Jshulgach/Desktop-Arm/CAD Models/16-x-2-lcd-display-module/Lcd6.jpg

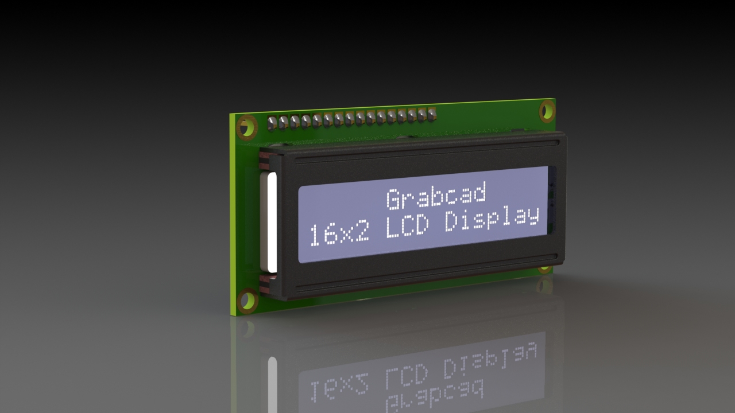
CAD Models/16-x-2-lcd-display-module/Lcd6.jpg
