Jshulgach/Desktop-Arm/CAD Models/ac-power-outlet-socket/AC Power Outlet Socket.PNG

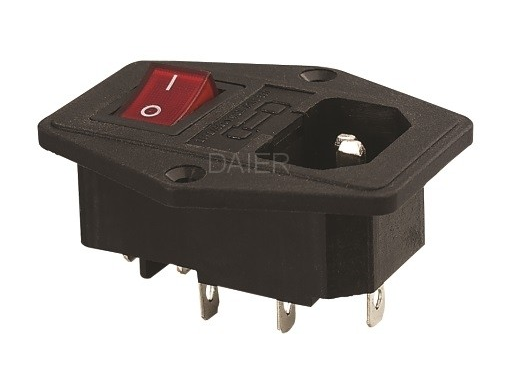
CAD Models/ac-power-outlet-socket/AC Power Outlet Socket.PNG
