Jshulgach/Desktop-Arm/CAD Models/arduino-mega-ramps-1-4/ARDUINO MEGA + RAMPS 1.4/mega-ramps-a49881.jpg

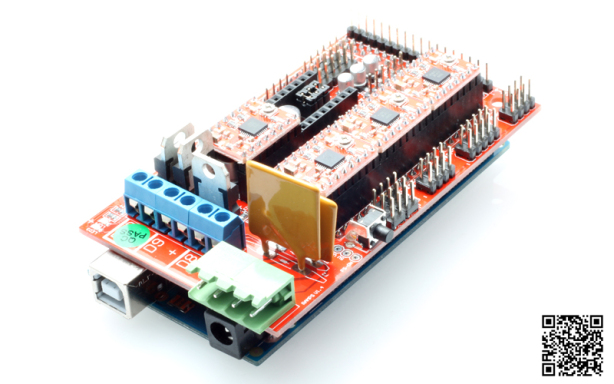
CAD Models/arduino-mega-ramps-1-4/ARDUINO MEGA + RAMPS 1.4/mega-ramps-a49881.jpg
