Jshulgach/Desktop-Arm/CAD Models/raspberry-pi-4-model-b/Broadcom BCM54213PE Gigabit Ethernet Transceiver, RPi4ModelB.SLDPRT

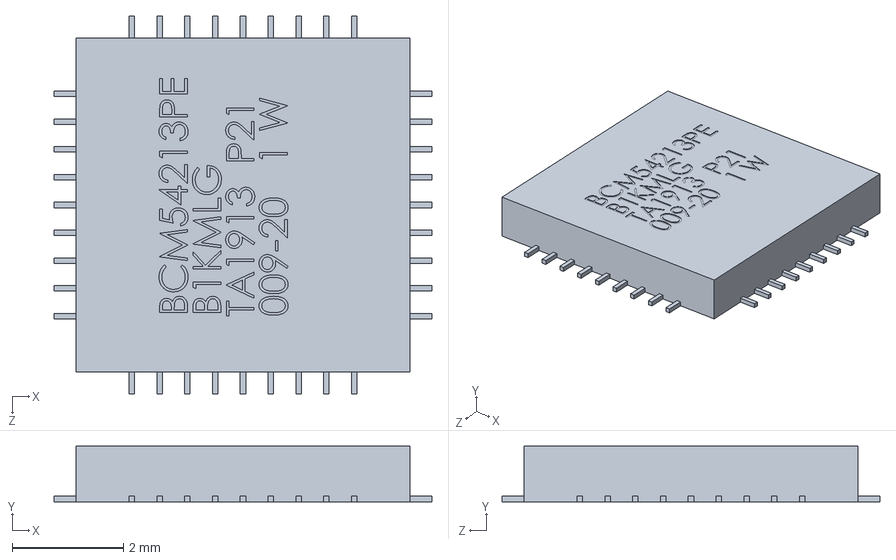
[picture p22: CAD file, 2022-05-16]
CAD Models/raspberry-pi-4-model-b/Broadcom BCM54213PE Gigabit Ethernet Transceiver, RPi4ModelB.SLDPRT
6.80 x 1.00 x 6.80 mm
