Jshulgach/Desktop-Arm/robot_resources/Arduino Robot Arm 3D Model/Servo Motor Micro  9g.SLDPRT

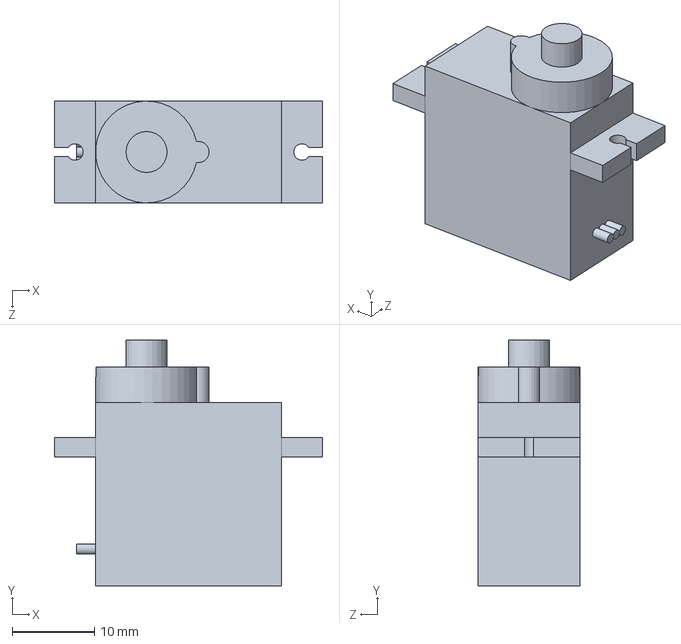
[picture p23: CAD file, 2021-09-17]
robot_resources/Arduino Robot Arm 3D Model/Servo Motor Micro 9g.SLDPRT
32.6 x 29.9 x 12.4 mm
