Jshulgach/Desktop-Arm/robot_resources/desktop_arm_description/meshes/link_5.STL

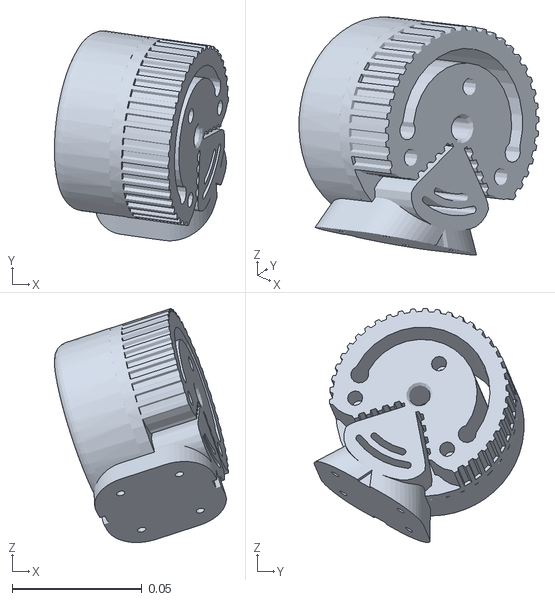
[picture p24: CAD file, 2022-05-21]
robot_resources/desktop_arm_description/meshes/link_5.STL
0.0672 x 0.081 x 0.0903
