Jshulgach/Desktop-Arm/CAD Models/desktop_arm_base.SLDPRT

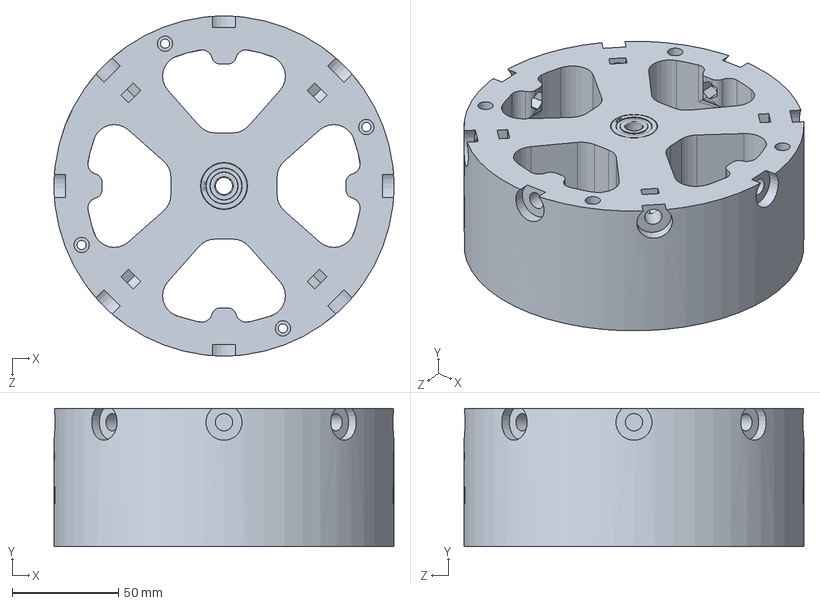
[picture p25: CAD file, 2022-05-21]
CAD Models/desktop_arm_base.SLDPRT
160.0 x 65.0 x 160.0 mm
