Jshulgach/Desktop-Arm/CAD Models/PSU Box/Raspi Shelf.SLDPRT

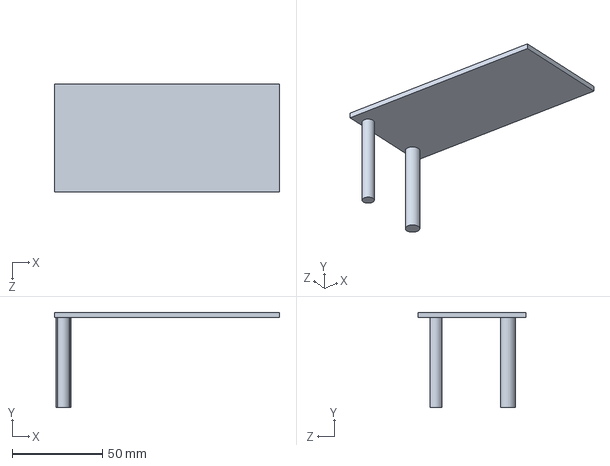
[picture p26: CAD file, 2022-05-16]
CAD Models/PSU Box/Raspi Shelf.SLDPRT
125.0 x 53.0 x 60.0 mm
