Jshulgach/Desktop-Arm/CAD Models/raspberry-pi-4-model-b/Female USB Type C Connector, RPi4ModelB.SLDPRT

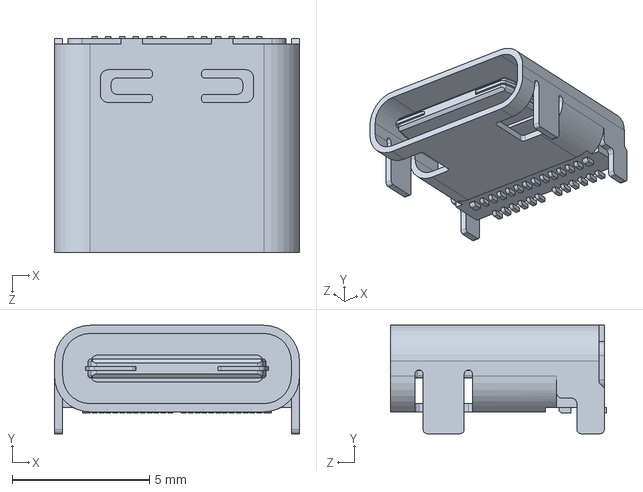
[picture p27: CAD file, 2022-05-16]
CAD Models/raspberry-pi-4-model-b/Female USB Type C Connector, RPi4ModelB.SLDPRT
8.94 x 3.96 x 7.90 mm
