Jshulgach/Desktop-Arm/robot_resources/Arduino Robot Arm 3D Model/Gripper/Gripper base.SLDPRT

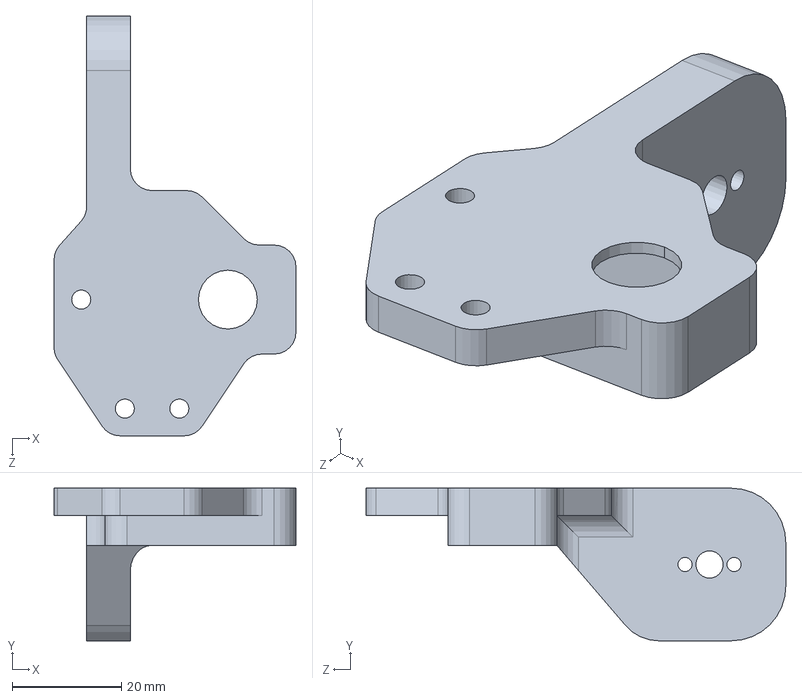
[picture p28: CAD file, 2021-09-17]
robot_resources/Arduino Robot Arm 3D Model/Gripper/Gripper base.SLDPRT
44.4 x 28.0 x 77.0 mm
