Jshulgach/Desktop-Arm/robot_resources/desktop_arm_description/meshes/base_link.STL

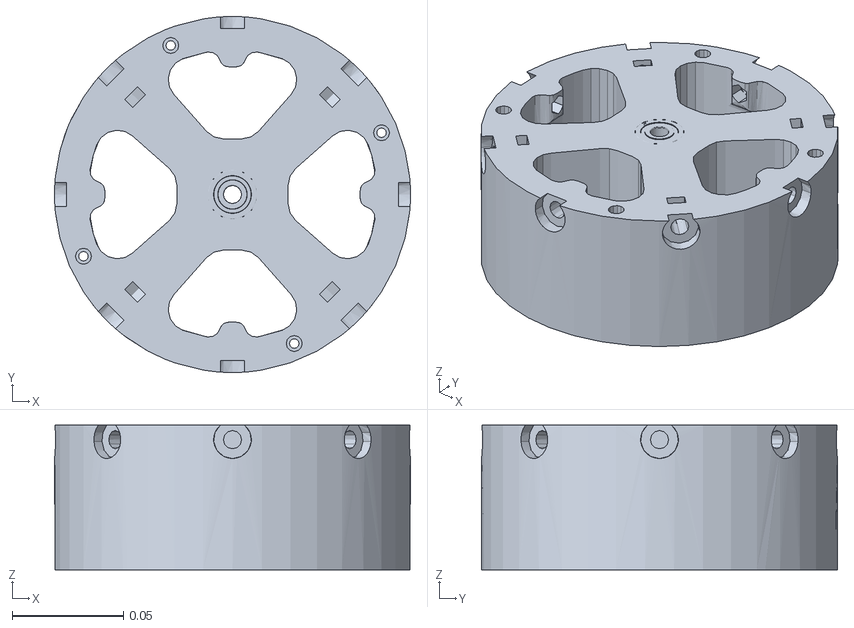
[picture p29: CAD file, 2022-05-21]
robot_resources/desktop_arm_description/meshes/base_link.STL
0.16 x 0.16 x 0.065
