Jshulgach/Desktop-Arm/CAD Models/raspberry-pi-4-model-b/Cypress CYW43455 Wireless Module Cover, RPi4ModelB.SLDPRT

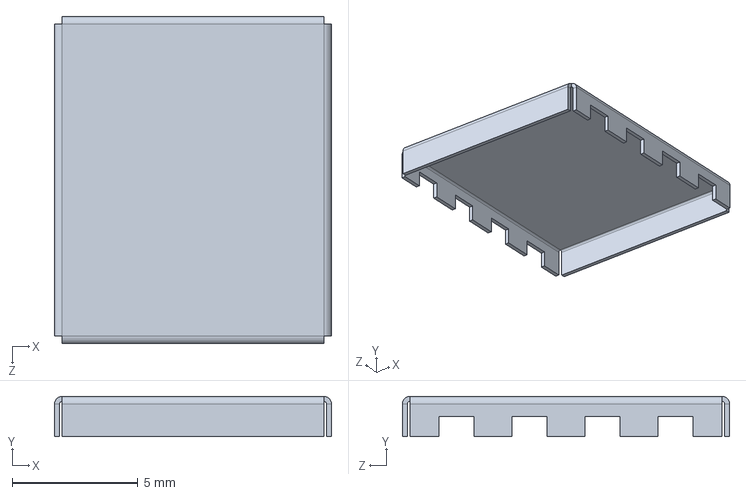
[picture p30: CAD file, 2022-05-16]
CAD Models/raspberry-pi-4-model-b/Cypress CYW43455 Wireless Module Cover, RPi4ModelB.SLDPRT
11.0 x 1.60 x 13.0 mm
