Jshulgach/Desktop-Arm/robot_resources/Arduino Robot Arm 3D Model/Test 01.SLDPRT

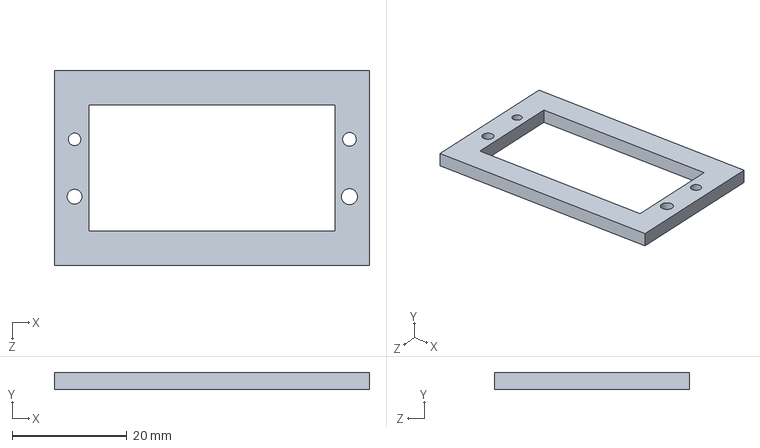
[picture p31: CAD file, 2021-09-17]
robot_resources/Arduino Robot Arm 3D Model/Test 01.SLDPRT
55.0 x 3.00 x 34.0 mm
