Jshulgach/Desktop-Arm/CAD Models/raspberry-pi-4-model-b/Camera Connector, RPi4ModelB.SLDPRT

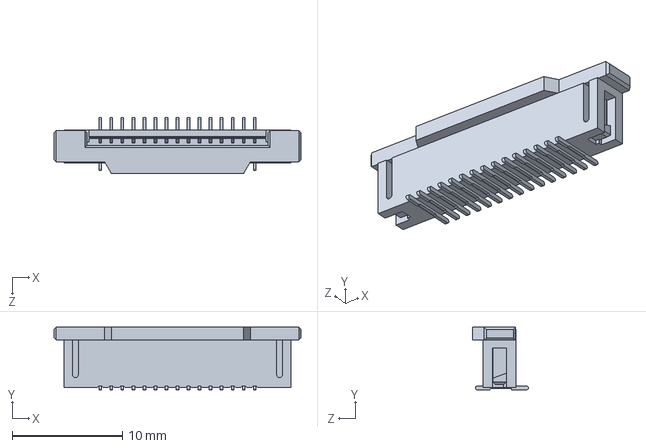
[picture p32: CAD file, 2022-05-16]
CAD Models/raspberry-pi-4-model-b/Camera Connector, RPi4ModelB.SLDPRT
22.4 x 5.68 x 5.07 mm
