Jshulgach/Desktop-Arm/robot_resources/Arduino Robot Arm 3D Model/Servo Motor MG996R_r1.SLDPRT

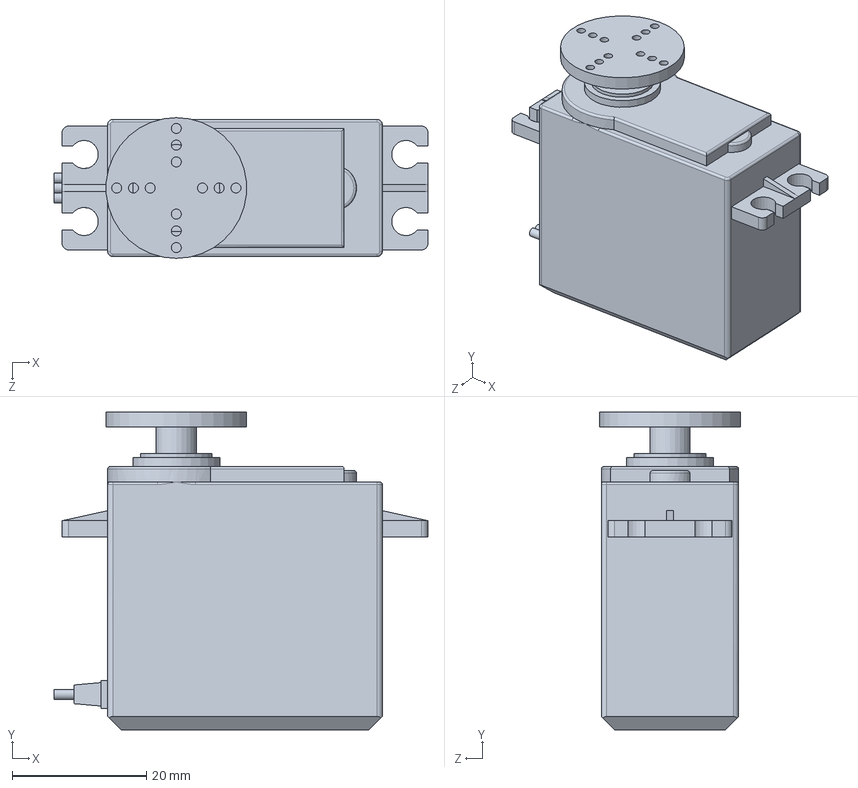
[picture p33: CAD file, 2021-09-17]
robot_resources/Arduino Robot Arm 3D Model/Servo Motor MG996R_r1.SLDPRT
55.8 x 47.4 x 21.0 mm
