Jshulgach/Desktop-Arm/CAD Models/raspberry-pi-4-model-b/2X USB3.0 PORTS, RPi4ModelB.SLDPRT

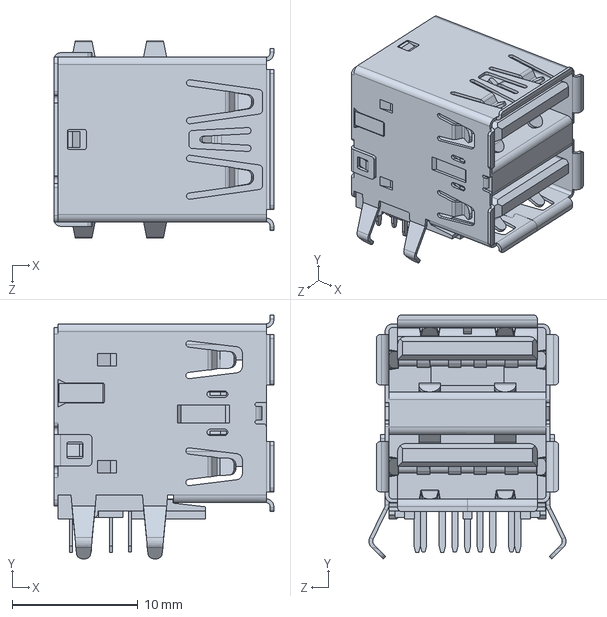
[picture p34: CAD file, 2022-05-16]
CAD Models/raspberry-pi-4-model-b/2X USB3.0 PORTS, RPi4ModelB.SLDPRT
17.5 x 19.4 x 15.7 mm
