Jshulgach/Desktop-Arm/robot_resources/Arduino Robot Arm 3D Model/Arm 03_r1.SLDPRT

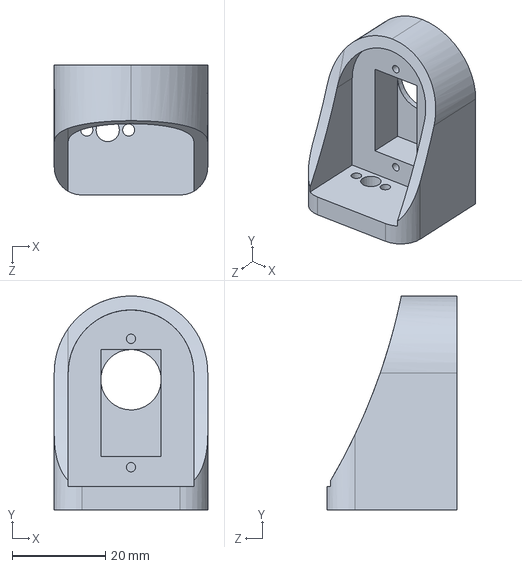
[picture p35: CAD file, 2021-09-17]
robot_resources/Arduino Robot Arm 3D Model/Arm 03_r1.SLDPRT
33.0 x 46.0 x 28.0 mm
