Jshulgach/Desktop-Arm/robot_resources/Arduino Robot Arm 3D Model/Gripper/gear1_r1.SLDPRT

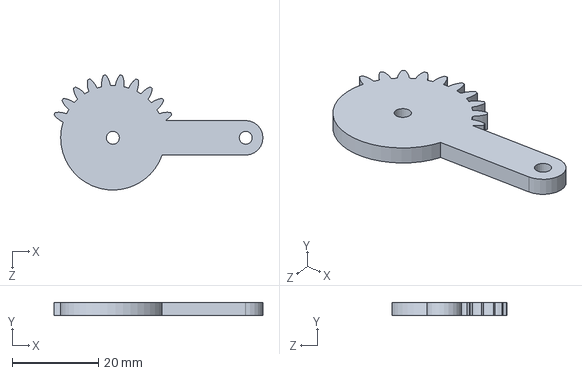
[picture p36: CAD file, 2021-09-17]
robot_resources/Arduino Robot Arm 3D Model/Gripper/gear1_r1.SLDPRT
48.4 x 3.00 x 26.6 mm
