Jshulgach/Desktop-Arm/CAD Models/raspberry-pi-4-model-b/SD Card Slot, RPi4ModelB.SLDPRT

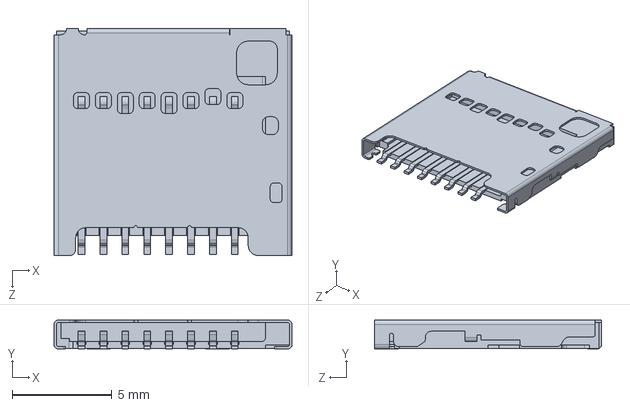
[picture p37: CAD file, 2022-05-16]
CAD Models/raspberry-pi-4-model-b/SD Card Slot, RPi4ModelB.SLDPRT
11.9 x 1.45 x 11.4 mm
