Jshulgach/Desktop-Arm/robot_resources/Arduino Robot Arm 3D Model/Arm 01_r1.SLDPRT

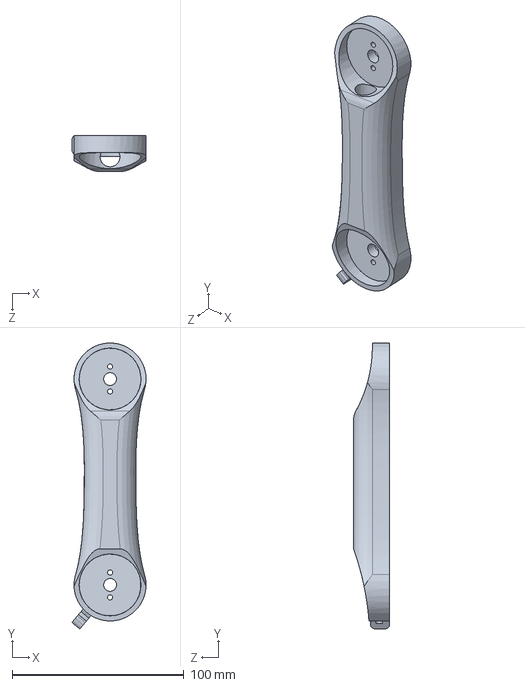
[picture p38: CAD file, 2021-09-17]
robot_resources/Arduino Robot Arm 3D Model/Arm 01_r1.SLDPRT
43.2 x 166.7 x 21.0 mm
