Jshulgach/Desktop-Arm/robot_resources/Arduino Robot Arm 3D Model/Gripper/Gripper 1_r1.SLDPRT

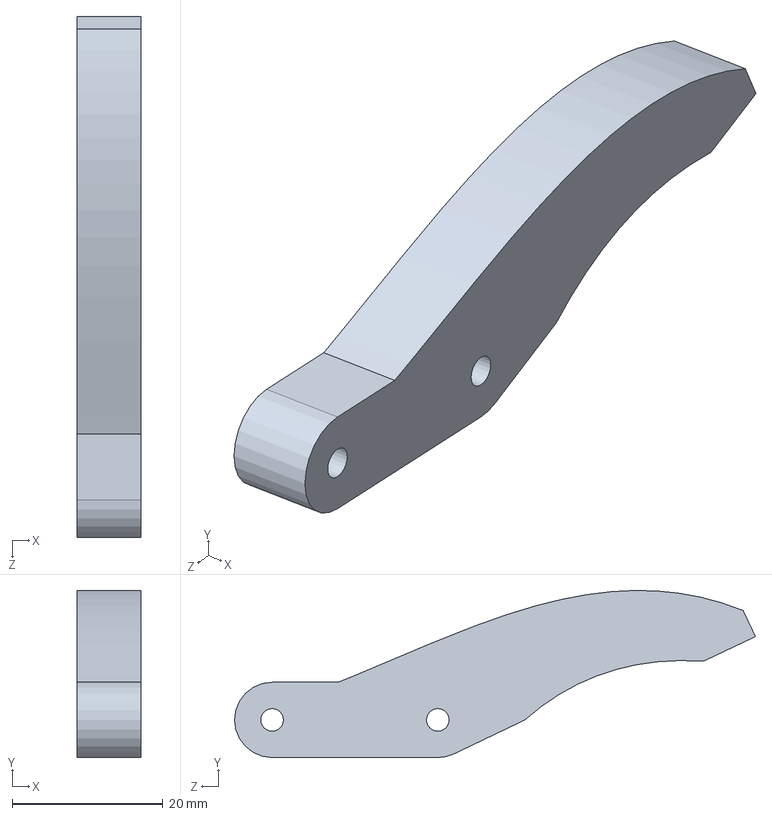
[picture p39: CAD file, 2021-09-17]
robot_resources/Arduino Robot Arm 3D Model/Gripper/Gripper 1_r1.SLDPRT
8.50 x 22.2 x 69.2 mm
