Jshulgach/Desktop-Arm/robot_resources/Arduino Robot Arm 3D Model/Arm 02 v3.SLDPRT

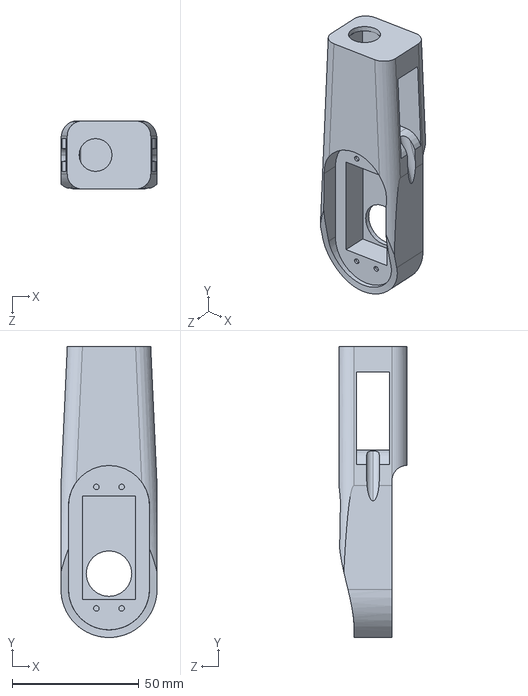
[picture p40: CAD file, 2021-09-17]
robot_resources/Arduino Robot Arm 3D Model/Arm 02 v3.SLDPRT
38.0 x 115.0 x 27.0 mm
