Jshulgach/Desktop-Arm/CAD Models/raspberry-pi-4-model-b/2X USB2.0 PORTS, RPi4ModelB.SLDPRT

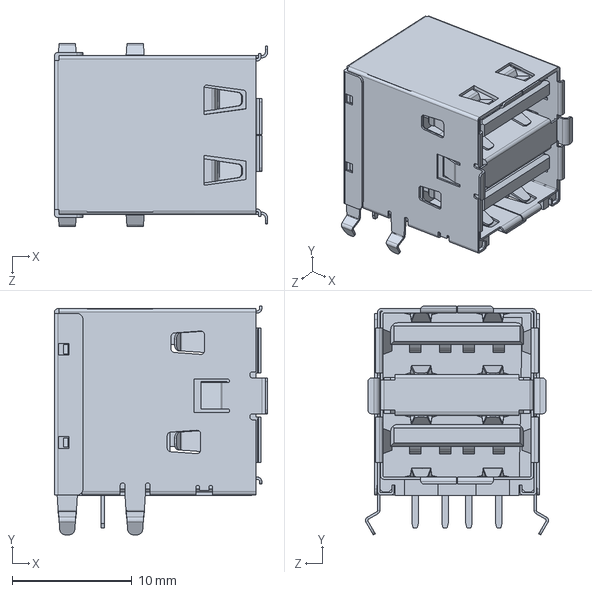
[picture p41: CAD file, 2022-05-16]
CAD Models/raspberry-pi-4-model-b/2X USB2.0 PORTS, RPi4ModelB.SLDPRT
17.9 x 19.2 x 15.3 mm
