Jshulgach/Desktop-Arm/robot_resources/Arduino Robot Arm 3D Model/Base_r1.SLDPRT

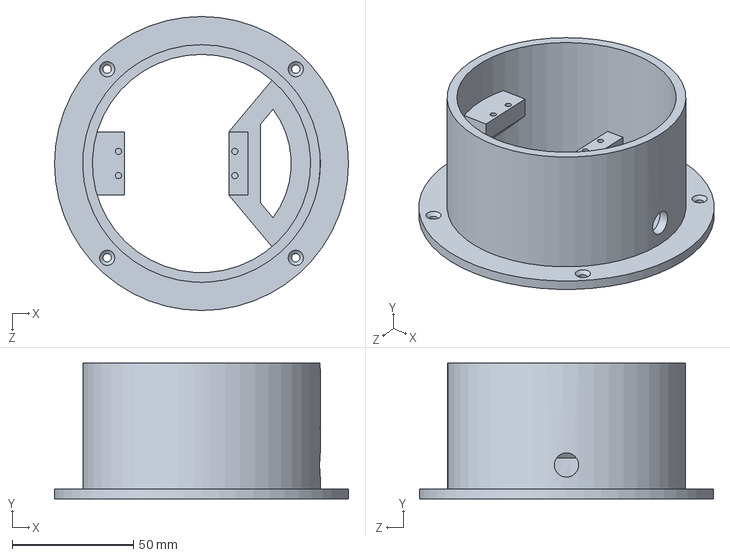
[picture p42: CAD file, 2021-09-17]
robot_resources/Arduino Robot Arm 3D Model/Base_r1.SLDPRT
121.2 x 56.0 x 121.2 mm
