Jshulgach/Desktop-Arm/robot_resources/Arduino Robot Arm 3D Model/Gripper/Gripper 1 v2.SLDPRT

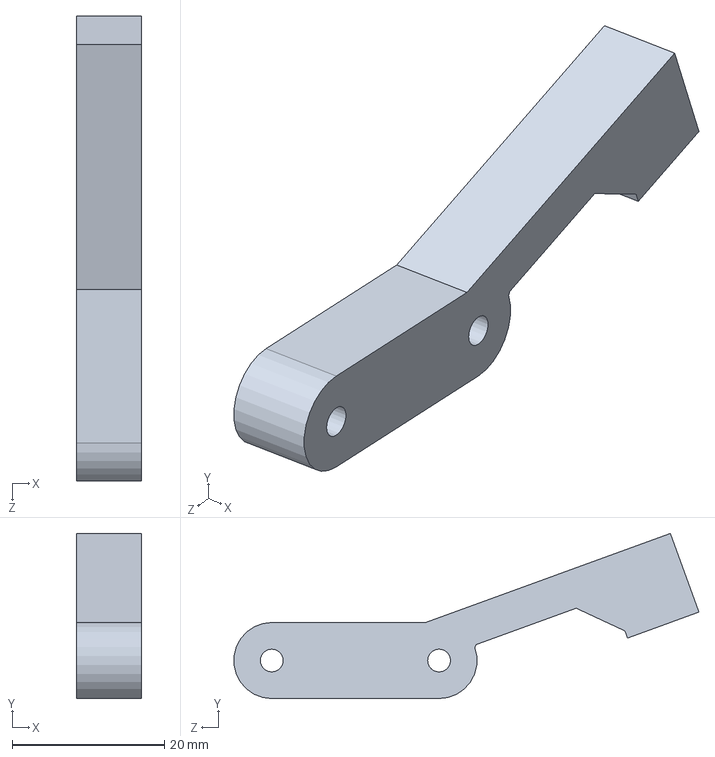
[picture p43: CAD file, 2021-09-17]
robot_resources/Arduino Robot Arm 3D Model/Gripper/Gripper 1 v2.SLDPRT
8.50 x 21.7 x 61.1 mm
