Jshulgach/Desktop-Arm/CAD Models/raspberry-pi-4-model-b/VIA VL805 PCIe USB 3.0 controller, RPi4ModelB.SLDPRT

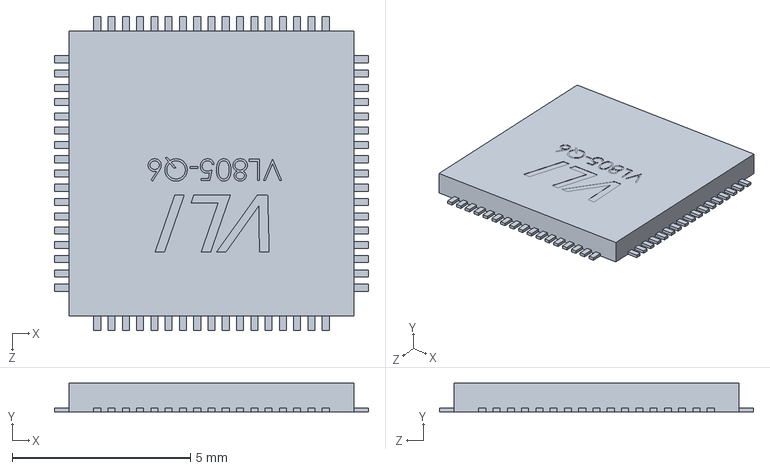
[picture p44: CAD file, 2022-05-16]
CAD Models/raspberry-pi-4-model-b/VIA VL805 PCIe USB 3.0 controller, RPi4ModelB.SLDPRT
8.80 x 0.8 x 8.80 mm
