Jshulgach/Desktop-Arm/robot_resources/Arduino Robot Arm 3D Model/Gripper/grip link 1.SLDPRT

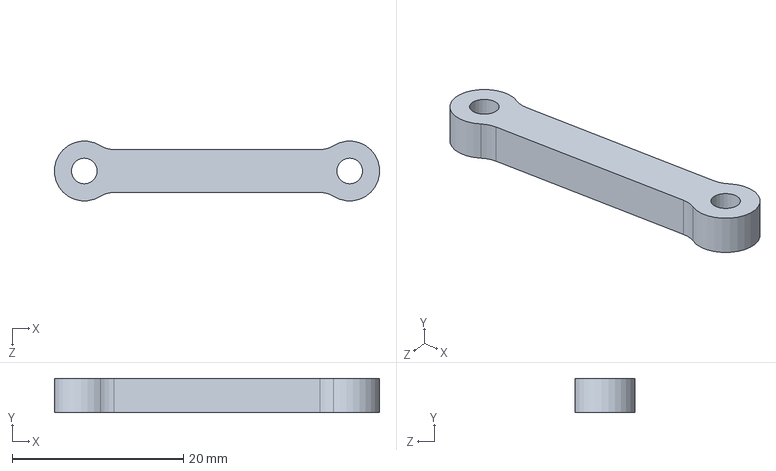
[picture p45: CAD file, 2021-09-17]
robot_resources/Arduino Robot Arm 3D Model/Gripper/grip link 1.SLDPRT
38.0 x 4.00 x 6.96 mm
