Jshulgach/Desktop-Arm/robot_resources/Arduino Robot Arm 3D Model/Waist_r1.SLDPRT

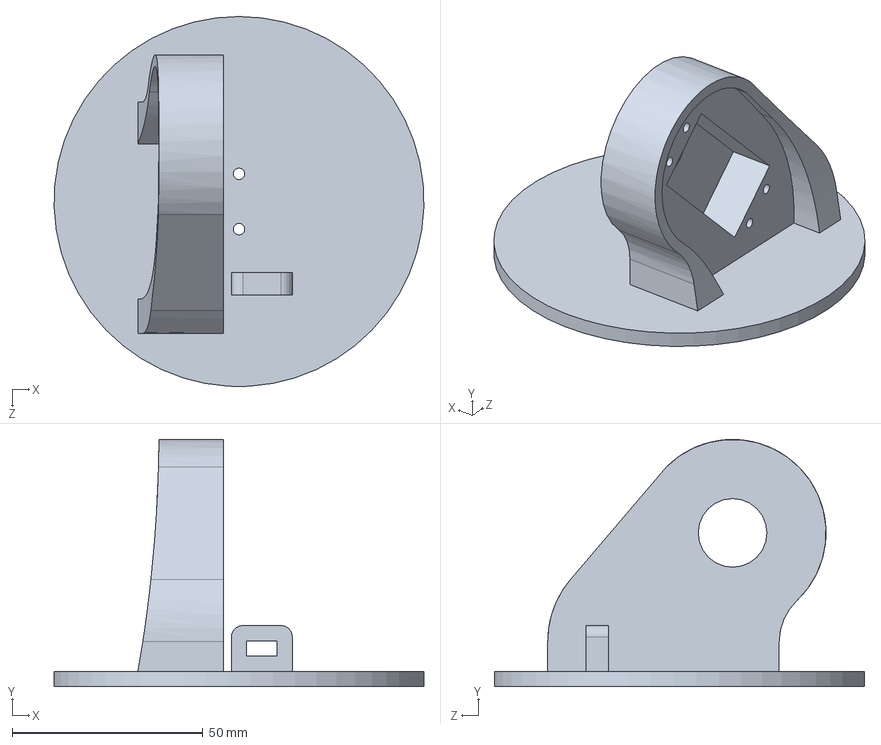
[picture p46: CAD file, 2021-09-17]
robot_resources/Arduino Robot Arm 3D Model/Waist_r1.SLDPRT
97.0 x 64.8 x 97.0 mm
