Jshulgach/Desktop-Arm/CAD Models/raspberry-pi-4-model-b/Female Micro HDMI Connector, RPi4ModelB.SLDPRT

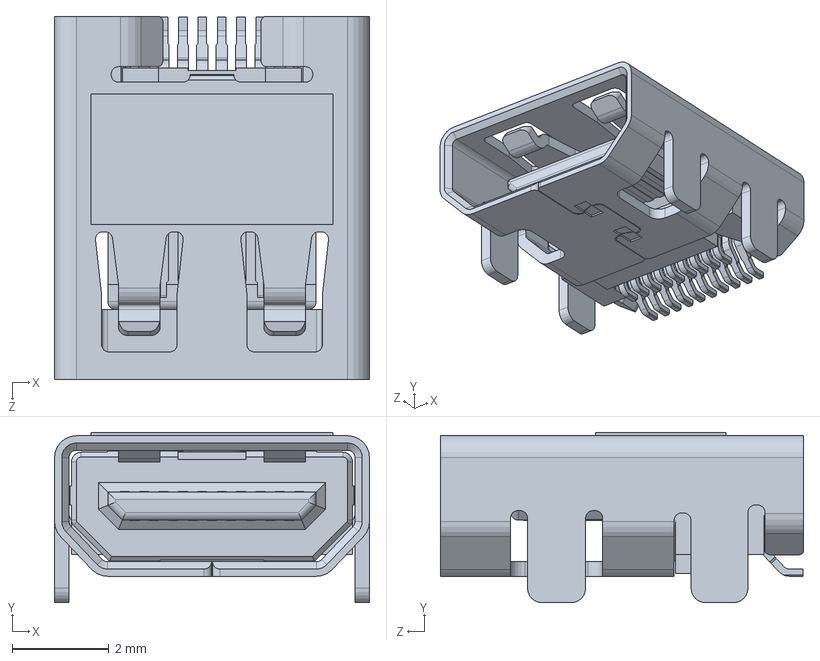
[picture p47: CAD file, 2022-05-16]
CAD Models/raspberry-pi-4-model-b/Female Micro HDMI Connector, RPi4ModelB.SLDPRT
6.50 x 3.52 x 7.50 mm
