Jshulgach/Desktop-Arm/CAD Models/raspberry-pi-4-model-b/PCB, RPi4ModelB.SLDPRT

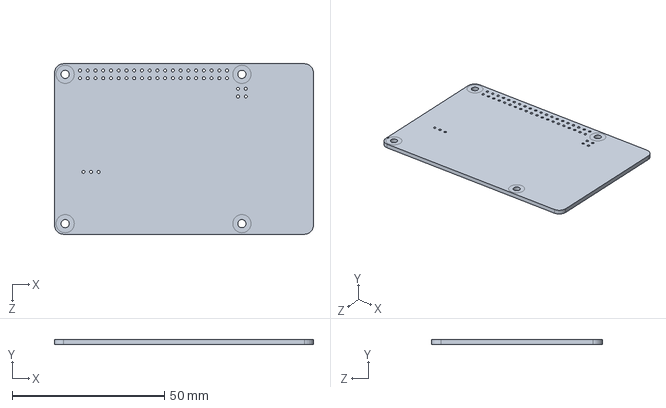
[picture p48: CAD file, 2022-05-16]
CAD Models/raspberry-pi-4-model-b/PCB, RPi4ModelB.SLDPRT
85.0 x 1.60 x 56.0 mm
