Jshulgach/Desktop-Arm/robot_resources/Arduino Robot Arm 3D Model/Arm 02.SLDPRT

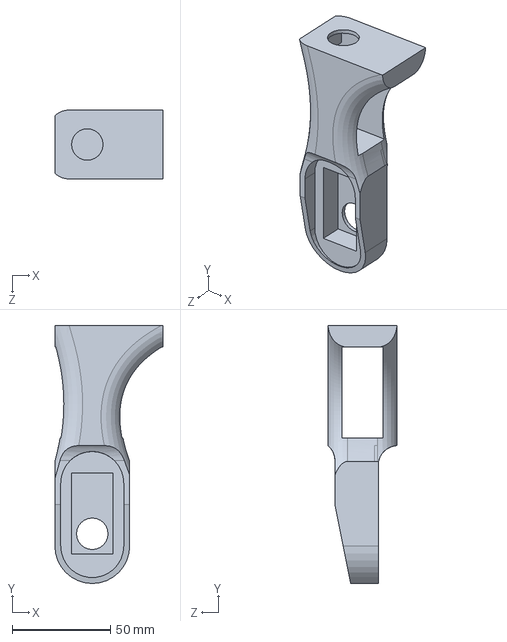
[picture p49: CAD file, 2021-09-17]
robot_resources/Arduino Robot Arm 3D Model/Arm 02.SLDPRT
55.0 x 131.0 x 35.0 mm
