Jshulgach/Desktop-Arm/CAD Models/raspberry-pi-4-model-b/Gigabit Ethernet Port, RPi4ModelB.SLDPRT

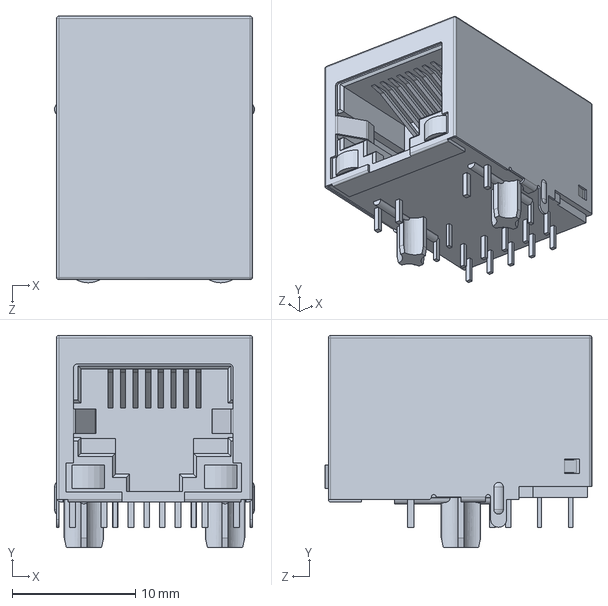
[picture p50: CAD file, 2022-05-16]
CAD Models/raspberry-pi-4-model-b/Gigabit Ethernet Port, RPi4ModelB.SLDPRT
16.2 x 17.2 x 21.6 mm
