Jshulgach/Desktop-Arm/CAD Models/raspberry-pi-4-model-b/Microphone Plug, RPi4ModelB.SLDPRT

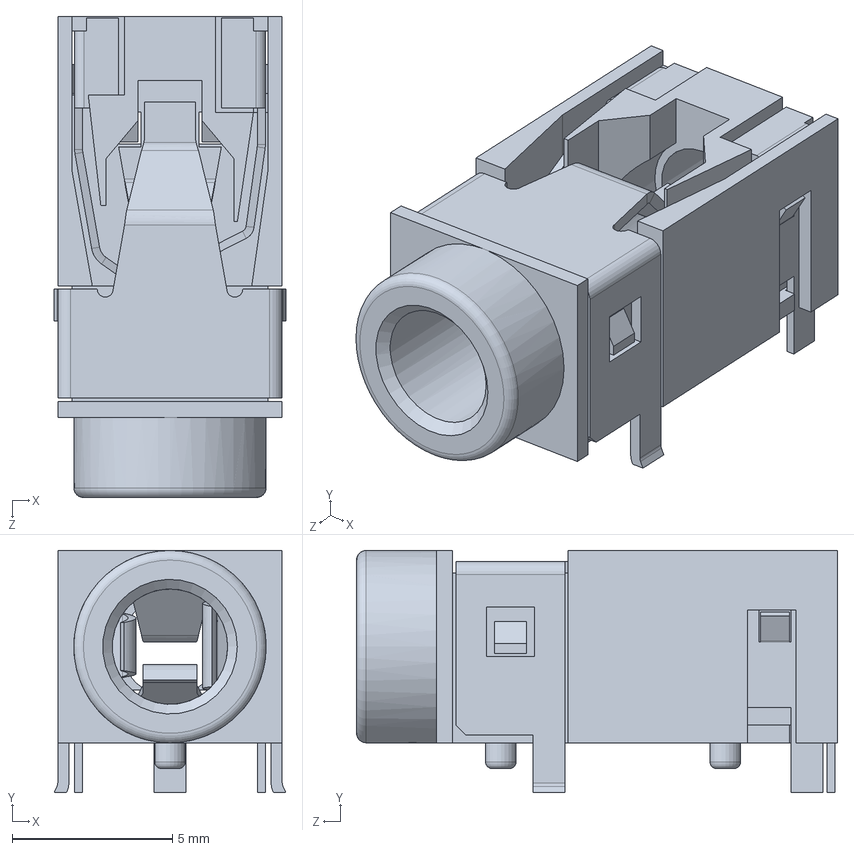
[picture p51: CAD file, 2022-05-16]
CAD Models/raspberry-pi-4-model-b/Microphone Plug, RPi4ModelB.SLDPRT
7.23 x 7.55 x 15.0 mm
