Jshulgach/Desktop-Arm/CAD Models/raspberry-pi-4-model-b/Broadcom BCM2711B0 CPU, RPi4ModelB.SLDPRT

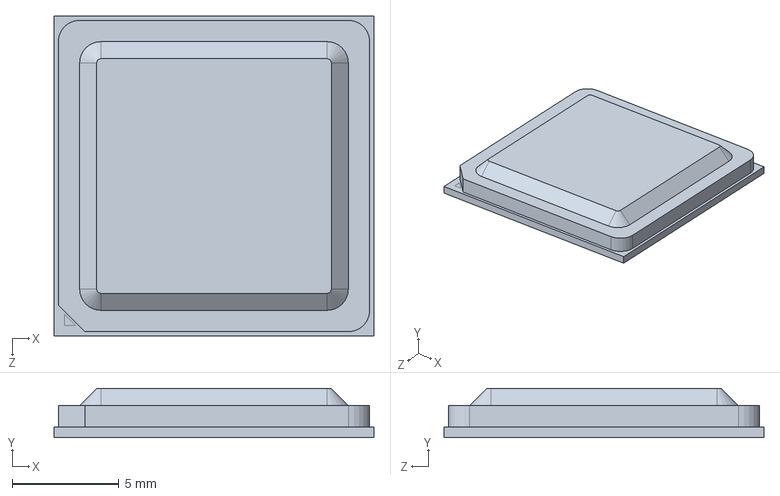
[picture p52: CAD file, 2022-05-16]
CAD Models/raspberry-pi-4-model-b/Broadcom BCM2711B0 CPU, RPi4ModelB.SLDPRT
15.0 x 2.30 x 15.0 mm
