Jshulgach/Desktop-Arm/CAD Models/raspberry-pi-4-model-b/MxL7704 Universal PMIC, RPi4ModelB.SLDPRT

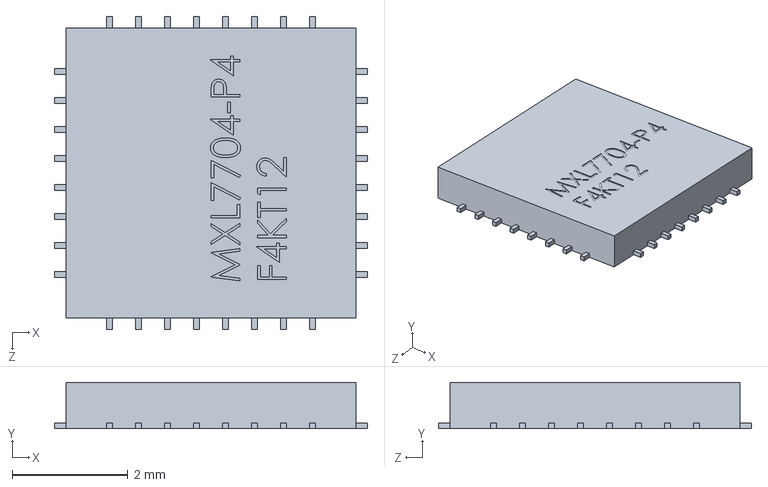
[picture p53: CAD file, 2022-05-16]
CAD Models/raspberry-pi-4-model-b/MxL7704 Universal PMIC, RPi4ModelB.SLDPRT
5.40 x 0.8 x 5.40 mm
