Jshulgach/Desktop-Arm/CAD Models/raspberry-pi-4-model-b/2.54 mm DUPONT MALE PIN HEADER, POE, 2X2, RPi4ModelB.SLDPRT

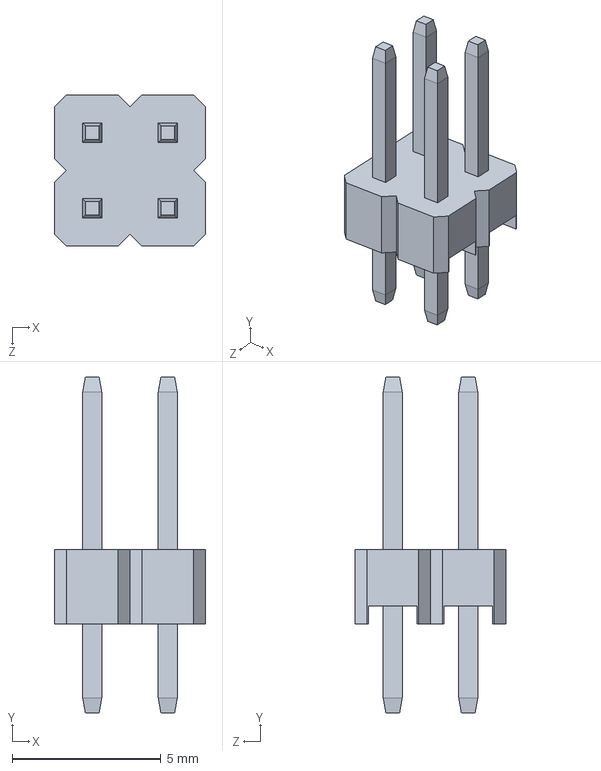
[picture p54: CAD file, 2022-05-16]
CAD Models/raspberry-pi-4-model-b/2.54 mm DUPONT MALE PIN HEADER, POE, 2X2, RPi4ModelB.SLDPRT
5.08 x 11.3 x 5.08 mm
