Jshulgach/Desktop-Arm/CAD Models/raspberry-pi-4-model-b/91D77 D9WHV 778K, 4 GB LPDDR4 SDRAM, RPi4ModelB.SLDPRT

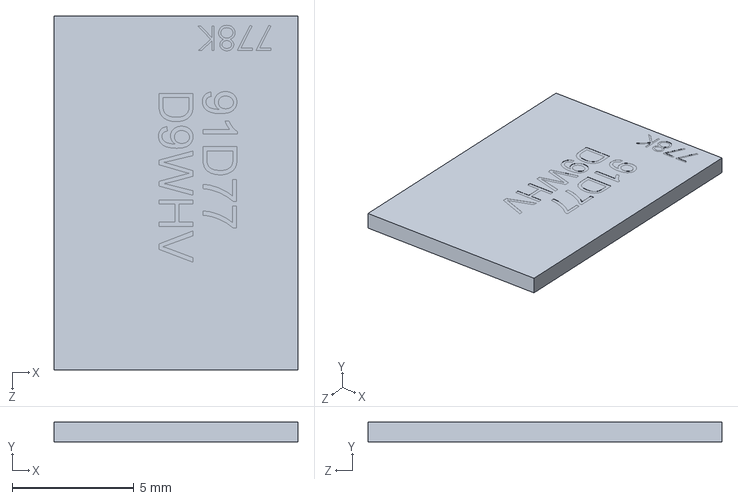
[picture p55: CAD file, 2022-05-16]
CAD Models/raspberry-pi-4-model-b/91D77 D9WHV 778K, 4 GB LPDDR4 SDRAM, RPi4ModelB.SLDPRT
10.0 x 0.8 x 14.5 mm
