Jshulgach/Desktop-Arm/desktop_arm/desktop_arm/arm_drivers.py

#!/usr/bin/env python3
"""
Copyright 2022 Jonathan Shulgach

This Source Code Form is subject to the terms of the Mozilla Public
License, v. 2.0. If a copy of the MPL was not distributed with this
file, You can obtain one at https://mozilla.org/MPL/2.0/.

Contact: Jonathan Shulgach (jonathan@shulgach.com)

Messy collection of controller types and enums ... 

"""
# ROS libraries
import rclpy
from std_msgs.msg import Int32
from sensor_msgs.msg import Joy, JointState
from control_msgs.msg import JointJog
from geometry_msgs.msg import Twist, TwistStamped
from xbox_control import XINPUT_CODE_MAP

controllerTypes = {
    1: "keyboard",
    2: "xbox",
    }

controllerTopics = {
    "keyboard":"cmd_vel",
    "xbox":"/joy",
    }

robotStateTypes = {
    "joint_state":1,
    "joint_jog":2,
    "twist":3,
    }

STICK_TRANS_X = 0 # 0
STICK_TRANS_Y = 1 # 1
STICK_TRANS_Z = 2 # originally positive
STICK_ANGULAR_X = 3
STICK_ANGULAR_Y = 4
STICK_ANGULAR_Z = 5

XBOX_BASE_LEFT = 2
XBOX_BASE_RIGHT = 5


def convertSpacenavToCmd(self, msg, twist_msg, joint_msg):
        """ Function that converts spacemouse commands to twist or joint messages
        
        Notes:
        ------
        TO-DO - new controllers won't be added on until camera streaming is working
        """
        
        twist_msg.twist.linear.x = msg.axes[STICK_TRANS_X]
        twist_msg.twist.linear.y = msg.axes[STICK_TRANS_Y]
        twist_msg.twist.linear.z = msg.axes[STICK_TRANS_Z]

        twist_msg.twist.angular.x = msg.axes[STICK_ANGULAR_X]
        twist_msg.twist.angular.y = msg.axes[STICK_ANGULAR_Y]
        twist_msg.twist.angular.z = msg.axes[STICK_ANGULAR_Z]

        return True, twist_msg, joint_msg


class KeyboardController:
    def __init__(self, parent=None, operation_type=None, controller_info=None):
        """ The keyboard controller class that has all the methods and properties 
        a keyboard controller should have!
        
        Parameters:
        -----------
        parent : object
           The inherited RobotRontroller class
        operation_type : Enum
            Robot command message type 
        controller_into : str
            Keyboard ot joystick controller configured
            
        """
        self.parent.logger("Keyboard Controller")
        self.info = {"joint_pub_type": JointState, 
                     "joint_pub_topic": "/joint_states", 
                     "cmd_sub_type": Twist, 
                     "cmd_sub_topic": "/cmd_vel",
                     "gripper_sub_type": Int32,
                     "gripper_sub_topic": "gripper_state"}
        self.parent = parent # In case parameters need to be shared between the main driver and the user controller
        self.use_twist = False
        self.twist_msg = None
        self.joint_msg = None

        if operation_type==robotStateTypes["twist"]:
            self.twist_msg = TwistStamped()
            if (self.parent is not None):
                self.parent.logger("Twist commands not suppoted yet for this controller")
        
        elif operation_type==robotStateTypes["joint_jog"]:
            if (self.parent is not None):
                self.parent.logger("Joint Jogging not supported yet for this controller")
        
        elif operation_type==robotStateTypes["joint_state"]:
            self.joint_msg = JointState()
            self.parent.logger("Creating JointState type for Keyboard controller")

        else:
            if self.parent:
                self.parent.logger("Invalid operation type passed. User controller failed set up.")

        if self.parent:
            self.pub = self.parent.create_publisher(self.info['pub_type'], self.info['pub_topic'], 10)
            self.sub = self.parent.create_subscription(self.info['sub_type'], self.info['sub_topic'], self.sub_CB, 10)


    def sub_CB(self, msg):
        """ Convert the keyboard message to Twist or JointJog (or JointState!) and publish
        
        Parameters:
        -----------
        msg : Twist
            Latest message received from the '/cmd_vel' ROS2 topic
        
        """
        #twist_msg, joint_msg = self.create_ros_msg()
        self.use_twist, self.twist_msg, self.joint_msg = self.convertKeyboardToCmd(msg, self.twist_msg, self.joint_msg, self.parent.robot_state_type)
        
        
    def create_ros_msg(self):
        """ Helper function to create new ROS2 message types
        """
        twist_msg = TwistStamped()
        if self.parent.robot_state_type == robotStateTypes["joint_state"]:
            joint_msg = JointState()
        else:
            joint_msg = JointJog()
        return twist_msg, joint_msg
                

    def convertKeyboardToCmd(self, msg, twist_msg, joint_msg, operation_type=robotStateTypes["joint_state"]):
        """ Function that converts the keyboard input message into the ROS2 robot command message
        
        Parameters:
        -----------
        msg : ROS2 msg
             ROS2 message received from the subscribed ROS2 topic callback function, converted into the new command message
        twist_msg : Twist 
            Twist ROS2 data type passed from the object
        joint_msg : JointState, JointJog 
            JointState or JointJog ROS2 data type passed from the object
        operation_type : enum
            Enum or int selection for the command message type
        
        Returns:
        --------
        use_twist : bool
            boolean passed which determines whether to use the twist or joint message publisher 
        twist_msg : Twist 
            Twist ROS2 data type passed from the object
        joint_msg : JointState, JointJog 
            JointState or JointJog ROS2 data type passed from the object
        
        Notes:
        ------
        
        
        """
        use_twist = False        
        if operation_type==robotStateTypes["twist"]:
            use_twist=True
            # map buttons to twist commands (keyboard only uses twist right now)
            self.twist_msg.linear.z = msg.linear.z
            self.twist_msg.linear.y = msg.linear.y
            self.twist_msg.linear.x = msg.linear.x

            self.twist_msg.angular.y = msg.angular.y
            self.twist_msg.angular.x = msg.angular.x
            self.twist_msg.angular.z = msg.angular.z
            self.parent.logger("twist not supported yet")
            
        elif operation_type==robotStateTypes["joint_jog"]:
            self.parent.logger("joint jog not supported yet")
            
        elif operation_type==robotStateTypes["joint_state"]:
            # Making this a JointState message type. 
            # It takes the controller inputs and converts them to new joint positions based on the previous positions 
          try:
            joint_msg.name = ["joint_1", "joint_2", "joint_3", "joint_4", "joint_5"]
            joint_msg.position = [msg.linear.x, msg.linear.y, msg.linear.z, msg.angular.x, msg.angular.y]
            #self.logger("new joint values: {}".format(joint_msg.position))
          except:
            self.parent.logger("something went wrong")


        return use_twist, twist_msg, joint_msg

    def update(self):
        """ Function that publishes the ROS2 message to either the twist or joint message 
        command type
        
        """
        if self.use_twist:
            # publish the TwistStamped
            if self.twist_msg is not None:
                self.twist_msg.header.frame_id = self.parent.frame_to_publish
                self.twist_msg.header.stamp = self.parent.get_clock().now().to_msg()
                self.parent.twist_pub.publish(self.twist_msg)
        else:
            # publish the JointState message
            if self.joint_msg is not None:
                #self.parent.logger("Publishing {} to topic {}".format(self.joint_msg.position, self.info['pup_topic']))
                self.joint_msg.header.frame_id = self.parent.frame_to_publish
                self.joint_msg.header.stamp = self.parent.get_clock().now().to_msg()
                self.parent.joint_pub.publish(self.joint_msg)

        return self.joint_msg.position, self.joint_msg.position


class XboxController:
    def __init__(self, parent=None, operation_type=None, controller_info=None):
        """ The xbox controller class that has all the methods and properties
        an xbox controller should have!

        Parameters:
        -----------
        parent : object
           The inherited RobotRontroller class
        operation_type : Enum
            Robot command message type 
        controller_into : str
            Keyboard ot joystick controller configured (not needed)

        """
        self.info = {"joint_pub_type": JointState,
                     "joint_pub_topic": "/joint_states",
                     "cmd_sub_type": Joy,
                     "cmd_sub_topic": "/joy",
                     "grip_pub_type":Int32,
                     "grip_pub_topic":"gripper_state"}
        self.parent = parent # In case parameters need to be shared between the main driver and the user controller
        self.use_twist = False
        self.twist_msg = None
        self.joint_msg = None
        self.prev_grip_state = 0

        if operation_type==robotStateTypes["twist"]:
            if (self.parent is not None):
                self.parent.logger("Twist commands not suppoted yet for this controller")

        elif operation_type==robotStateTypes["joint_jog"]:
            self.joint_msg = JointJog()
            if (self.parent is not None):
                self.parent.logger("Joint Jogging not supported yet for this controller")
        
        elif operation_type==robotStateTypes["joint_state"]:
            self.joint_msg = JointState()
            self.parent.logger("Creating JointState type for controller")
            
            if (self.parent is not None):
                self.cmd_sub = self.parent.create_subscription( self.info["cmd_sub_type"], self.info["cmd_sub_topic"], self.sub_CB, 10)
                self.joint_pub = self.parent.create_publisher( self.info["joint_pub_type"], self.info["joint_pub_topic"], 10)
                self.grip_pub = self.parent.create_publisher(self.info["grip_pub_type"], self.info["grip_pub_topic"], 1)
        else:
            if self.parent:
                self.parent.logger("Invalid operation type passed. User controller failed set up.")
                
        
    def sub_CB(self, msg):
        """ Convert the joystick message to Twist or JointJog (or JointState!) and publish
        
        Parameters:
        -----------
        msg : Twist
            Latest message received from the '/joy' ROS2 topic
        
        """
        self.use_twist, self.twist_msg, self.joint_msg = self.convertXboxToCmd(msg, self.twist_msg, self.joint_msg, self.parent.robot_state_type)
        
        
    def convertXboxToCmd(self, msg, twist_msg, joint_msg, operation_type=robotStateTypes["joint_state"]):
        """ Function that converts the controller input message into the ROS2 robot command message
        
        Parameters:
        -----------
        msg : ROS2 msg
             ROS2 message received from the subscribed ROS2 topic callback function, converted into the new command message
        twist_msg : Twist 
            Twist ROS2 data type passed from the object
        joint_msg : JointState, JointJog 
            JointState or JointJog ROS2 data type passed from the object
        operation_type : enum
            Enum or int selection for the command message type
        
        Returns:
        --------
        use_twist : bool
            boolean passed which determines whether to use the twist or joint message publisher 
        twist_msg : Twist 
            Twist ROS2 data type passed from the object
        joint_msg : JointState, JointJog 
            JointState or JointJog ROS2 data type passed from the object
        
        Notes:
        ------
        
        
        """
        use_twist = False
        if operation_type==robotStateTypes["twist"]:
            # map buttons to twist commands
            use_twist = True
            twist_msg.twist.linear.x = msg.axes[STICK_TRANS_X]
            twist_msg.twist.linear.y = msg.axes[STICK_TRANS_Y]
            twist_msg.twist.linear.z = msg.axes[STICK_TRANS_Z]
            twist_msg.twist.angular.x = msg.axes[STICK_ANGULAR_X]
            twist_msg.twist.angular.y = msg.axes[STICK_ANGULAR_Y]
            twist_msg.twist.angular.z = msg.axes[STICK_ANGULAR_Z]
            
        elif operation_type==robotStateTypes["joint_jog"]:
            # Making this a JointJog message type
            joint_msg.joint_names[0] = "joint_1"
            joint_msg.velocities[0] = msg.axes[0] # I think this is left joystick
            #elf.desired_joint_state = [0,0,0,0,0,0]
            
        elif operation_type==robotStateTypes["joint_state"]:
            """ Making this a JointState message type. It takes the controller inputs and converts them to new joint positions based on the previous positions 
                'ABS_X': 0,
            """
            joint_msg.name = ["joint_1", "joint_2", "joint_3", "joint_4", "joint_5"]
            
            # move up to 1 degree every step 
            stp = self.parent.joint_step
            joint_msg.position = [stp*msg.axes[0], stp*msg.axes[1], stp*msg.axes[3], stp*msg.axes[4], stp*msg.axes[5]]

            # Check gripper state and send gripper command 
            btn_press = msg.buttons[XINPUT_CODE_MAP['BTN_EAST']]
            msg = Int32()
            if btn_press == 1 and self.prev_grip_state == 0:
                self.prev_grip_state = 1
                msg.data = 1
                self.grip_pub.publish(msg)
            elif btn_press == 0 and self.prev_grip_state == 1:
                self.prev_grip_state = 0
                msg.data = 0
                self.grip_pub.publish(msg)

        return use_twist, twist_msg, joint_msg

    def update(self):
        """ Function that publishes the ROS2 message to either the twist or joint message 
        command type
        
        """
        if self.use_twist:
            # publish the TwistStamped
            self.twist_msg.header.frame_id = self.parent.frame_to_publish
            self.twist_msg.header.stamp = self.parent.get_clock().now().to_msg()
            self.twist_pub.publish(self.twist_msg)
        else:
            # publish the JointState message
            self.joint_msg.header.frame_id = self.parent.frame_to_publish
            self.joint_msg.header.stamp = self.parent.get_clock().now().to_msg()
            self.joint_pub.publish(self.joint_msg)

        return [0,0,0,0,0,0], [0,0,0,0,0,0]
            
            
            
