Jshulgach/Desktop-Arm/desktop_arm/desktop_arm/arduino_driver.py

#!/usr/bin/env python3
"""
Copyright 2022 Jonathan Shulgach

This Source Code Form is subject to the terms of the Mozilla Public
License, v. 2.0. If a copy of the MPL was not distributed with this
file, You can obtain one at https://mozilla.org/MPL/2.0/.

Contact: Jonathan Shulgach (jonathan@shulgach.com)


"""
import serial
import time
import math
from threading import Timer
import rclpy
from rclpy.node import Node
from sensor_msgs.msg import Joy, JointState
from std_msgs.msg import Int32

def radToDeg(val):
    """ Helper function to convert input radian value to degrees
    """
    return (val*180)/math.pi

def degToRad(val):
    """ Helper function to convert input degrees value to radians
    """
    return (val*math.pi)/180

class ArduinoTalker(Node):
    def __init__(self, node_name='arduino_node',
                       rate=30,
                       COM='/dev/ttyACM0',
                       baudrate=115200,
                       verbose=False
                ):
        """This class controls communication to the microcontroller handling stepper
        motor and gripper commands. It reads the data from the '/joint_state' ROS2 topic and converts
        it into the 'COMMAND:VALUE,VALUE,...' format

        Parameters:
        -----------
        node_name : str
            Specific name to register the ROS2 node
        rate : int
            Publishing rate to send data to the microcontroller
        COM : str
            The COM port that the microcontroller is on, usually 'tty/ACM0'
        baudrate : int
            The baudrate setting for microcontroller communication speed
        verbose : bool
            Enable/disable verbose output for debug on the terminal

        """
        super().__init__(node_name)
        self.rate = rate
        self.COM = COM
        self.baudrate = baudrate
        self.verbose = verbose
        self.step = 1
        self.grip_sub = self.create_subscription(Int32, "gripper_state", self.gripper_CB, 1)
        self.joint_sub = self.create_subscription(JointState, "joint_states", self.joint_state_CB, 1)
        self.joint_states = [0.0, 0.0, 0.0, 0.0, 0.0]
        self.prev_joint_states = [0.0, 0.0, 0.0, 0.0, 0.0]
        self.grip_state = 0
        self.prev_grip_state = 0
        self.last_msg = ''

        # Try to connect to device
        self.ser = None
        self.connected = False
        self.connect(self.COM, self.baudrate)
        self.pub_timer = self.create_timer(1/self.rate, self.command_timer_CB) # frequency rate of running commands
        self.read_timer = self.create_timer(0.1, self.read_callback)

    def connect(self, COM='/dev/ttyACM0', baudrate=115200):
        """ Function that attempts to connect to the port with selected baudrate

        Parameters:
        -----------
        COM : str
            The COM port that the microcontroller is on, usually 'tty/ACM0'
        baudrate : int
            The baudrate setting for microcontroller communication speed

        """
        if self.connected:
            self.logger("Already connected to {} with baudrate {}".format(self.COM, self.baudrate))

        while not self.connected:
            self.logger("Waiting for connection...")
            self.ser = serial.Serial(COM, baudrate, timeout=0.01)
            self.ser.reset_input_buffer()
            self.connected = True
            self.logger("Successful connection to {} with baudrate {}".format(COM, baudrate))
            #self.read(read_loop=10)


    def joint_state_CB(self, msg):
        """ Callback function when new data is published to the '/joint_state' topic

        Parameters:
        -----------
        msg : JointState
            ROS2 message used to get the most recent joint position 
        """
        try:
            #new_val = radToDeg(self.step*msg.position[0])
            #print(round(new_val))
            #print(type(radToDeg(self.step*msg/position[0])))
            self.joint_states = [round(radToDeg(self.step*pos)) for pos in msg.position]
            #self.logger(self.joint_states)
        except:
            self.logger("Error in joint state callback")


    def gripper_CB(self, msg):
        """ Callback function executes when a new value is published to the "gripper_state" topic
        Parameters:
        -----------
        msg : Int32
            ROS2 message used to get the most recent gripper state
        """
        try:
            self.grip_state = msg.data
        except:
            self.logger("Error in getting gripper state")


    def logger(self, msg):
        # Send message to terminal
        self.get_logger().info(str(msg))

    def read_callback(self):
        if self.ser.inWaiting() > 0:
            #print()
            #self.last_msg = self.ser.readline().decode('utf8')
            self.last_msg = self.ser.readline(self.ser.inWaiting()).decode('ascii')
            print(self.last_msg)

    def command_timer_CB(self):
        """ Callback function that executes at a specified rate from the objects' 'rate' parameter
        """

        # Handle new motor commands
        #print("joint state message: {}".format(self.joint_states))
        if True:
            if self.joint_states != self.prev_joint_states:
                self.moveMotor(self.joint_states)


        # Handle gripper commands
        if True:
            if self.grip_state != self.prev_grip_state:
                self.moveGripper(self.grip_state)


    def moveMotor(self, joint_states):
        # Send 'movemotor' command by checking each joint state and sending new positions
        for i in range(len(joint_states)):
            if self.joint_states[i] != self.prev_joint_states[i]:
                robot_msg = 'movemotor ' + str(i+1) + ' ' + str(joint_states[i]) + '\n'
                self.logger("Sending {} to Arduino".format(robot_msg))
                self.send(robot_msg, 'utf-8')
                self.prev_joint_states[i] = self.joint_states[i]

    def moveGripper(self, state):
                robot_msg = 'gripper ' + str(self.grip_state) + '\n'
                self.logger("Sending {} to Arduino".format(robot_msg))
                self.prev_grip_state = self.grip_state
                self.send(robot_msg, 'utf-8')


    def send(self, msg, msg_type='ascii'):
        """ Function that sends a string message to the connected serial port by 
        encoding it into a byte format first

        Parameters:
        -----------
        msg : str
            message to send to the serial port
        msg_type : str
            Encoding type for message before sending

        """
        self.ser.write(bytes(msg, msg_type))
        time.sleep(0.01)


    def read(self, msg_type='ascii', read_loop=1):
        """ Read the bytes and convert from binary array to ASCII
        """
        #self.ser.reset_input_buffer()
        #return

        for i in range(read_loop):
            #print("loop {}".format(i))
            if (self.ser.inWaiting() > 0):
                data_str = self.ser.readline().decode('utf-8')
                #data_str = self.ser.read(self.ser.inWaiting()).decode(msg_type)
                # print the incoming string without putting a new-line
                # ('\n') automatically after every print()
                print(data_str, end='')
                self.last_msg = data_str

                # Optional, but recommended: sleep 10 ms (0.01 sec) once per loop to let
                # other threads on your PC run during this time.
                #time.sleep(0.01)
                time.sleep(0.01)


def main(args=None):
    rclpy.init(args=args)
    node = ArduinoTalker()
    try:
        while rclpy.ok():
            rclpy.spin(node)
    except KeyboardInterrupt:
        pass

    finally:
        # Explicitly destroy node
        #node.timer.stop()
        node.destroy_node()
    #rclpy.shutdown()

if __name__=="__main__":
    main()
