Jshulgach/Desktop-Arm/desktop_arm/config/initial_positions.yaml

# Default initial positions for the desktop arm's ros2_control fake system
initial_positions:
  joint_1: 0.0
  joint_2: 0.0
  joint_3: 0.0
  joint_4: 0.0
  joint_5: 0.0
  joint_6: 0.0
